t0ry003/Series-Regulator-Voltage-Stabilizer-OrCad/Simulations/sim_bucla_deschisa.jpg

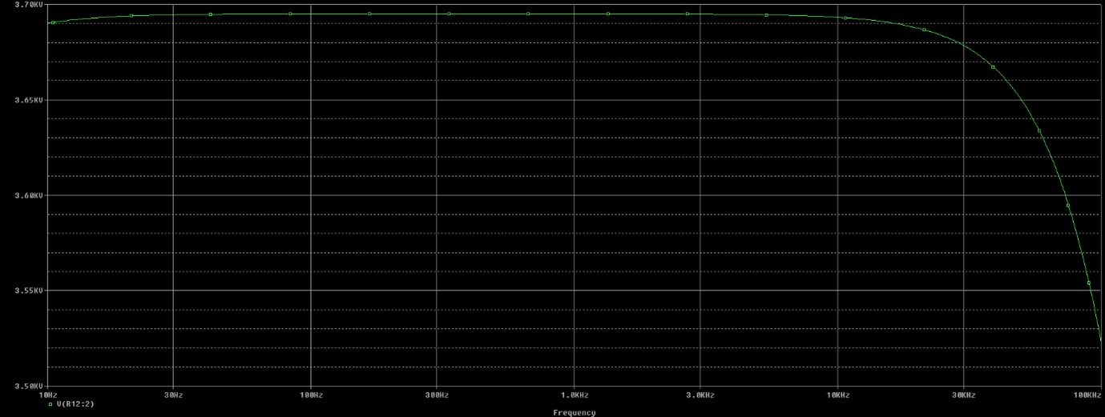
Simulations/sim_bucla_deschisa.jpg
