t0ry003/Series-Regulator-Voltage-Stabilizer-OrCad/Simulations/sim_temperatura.jpg

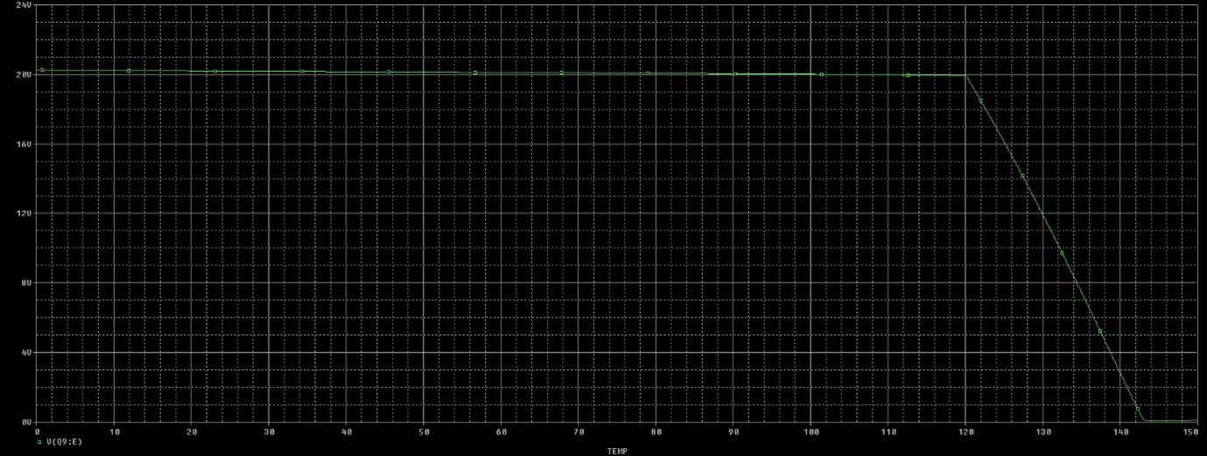
Simulations/sim_temperatura.jpg
