t0ry003/Series-Regulator-Voltage-Stabilizer-OrCad/Simulations/sim_tensiune.jpg

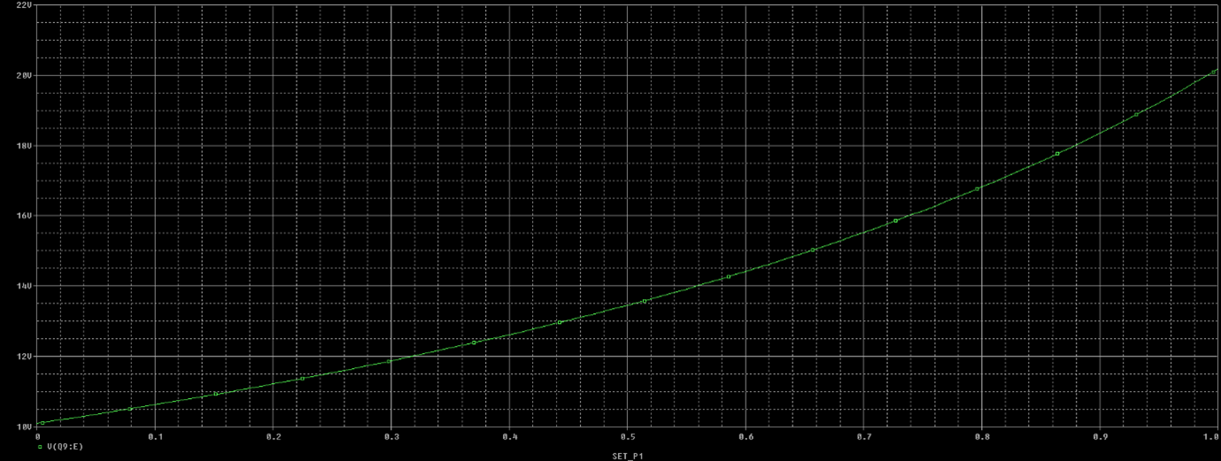
Simulations/sim_tensiune.jpg
